jamesweidev/tennis-robot/projects/01_obstacle_avoiding_robot/firmware/STM32_ObjectAvoider/Core/V1_BasicAvoidance/Inc/main.h

#ifndef MAIN_H_
#define MAIN_H_

#include <stdio.h>
#include <string.h>
#include "stm32f4xx_hal.h"

#define PWM_PERIOD              2500

#define US_GPIO_PORT			GPIOA
#define US_TRIG_PIN				GPIO_PIN_8
#define US_ECHO_PIN 			GPIO_PIN_9

#define PWM_RIGHT_GPIO_PORT		GPIOA
#define PWM_RIGHT_PIN			GPIO_PIN_0

#define PWM_LEFT_GPIO_PORT		GPIOA
#define PWM_LEFT_PIN			GPIO_PIN_1

#define MOTOR_DRIVER_IN_PORT	GPIOA

#define IN1_PIN					GPIO_PIN_6
#define IN2_PIN					GPIO_PIN_7
#define IN3_PIN					GPIO_PIN_4
#define IN4_PIN					GPIO_PIN_5

#define USART1_TX_PORT          GPIOB
#define USART1_TX_PIN           GPIO_PIN_6

// Directions
typedef enum
{
    ACTION_FORWARD,
    ACTION_REVERSE,
    ACTION_LEFT,
    ACTION_RIGHT,
    ACTION_STOP
} ActionType;

void Perform_Action(uint32_t speed, ActionType type);
void motor_direction_config(ActionType type);
void Stop_Robot();
uint32_t get_distance(void);
uint32_t micros(void);
void delay_us(uint32_t micros);

void Ultrasonic_GPIO_Init(void);
void TIM3_Micros_Init(void);
void PWM_Init(void);
void SystemClock_Config(void);

void UART1_Init(void);
void Error_Handler(void);

#endif
